la1k/la1k-cw-beacon/img/DSC_0003.jpg

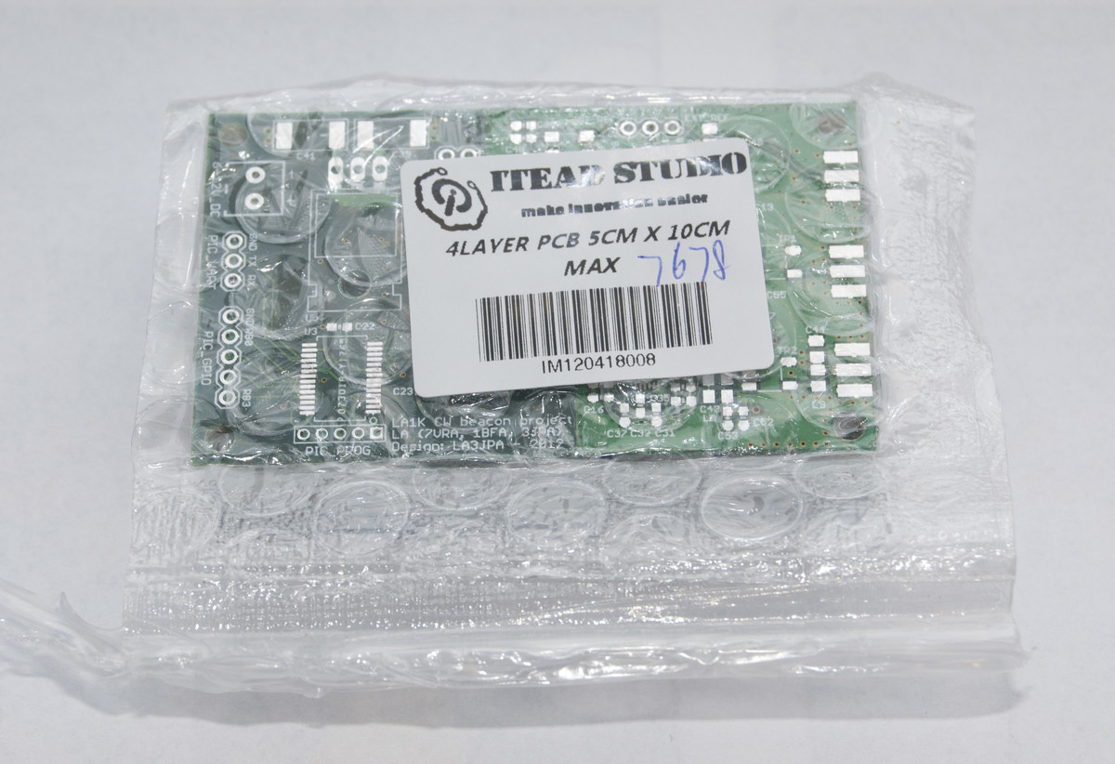
img/DSC_0003.jpg
