la1k/la1k-cw-beacon/img/DSC_0007.jpg

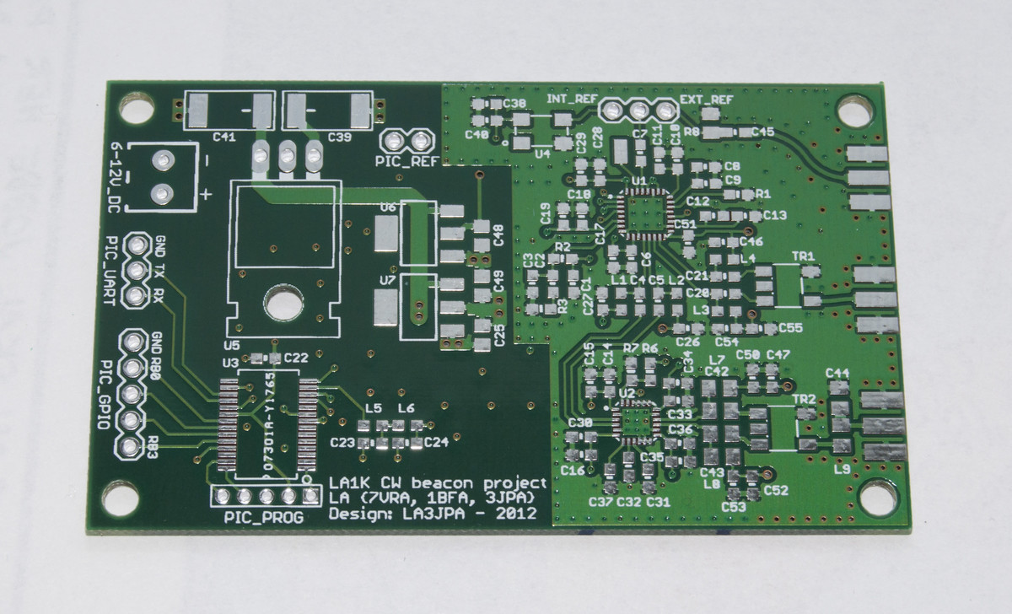
img/DSC_0007.jpg
