la1k/la1k-cw-beacon/img/IMAG1740.jpg

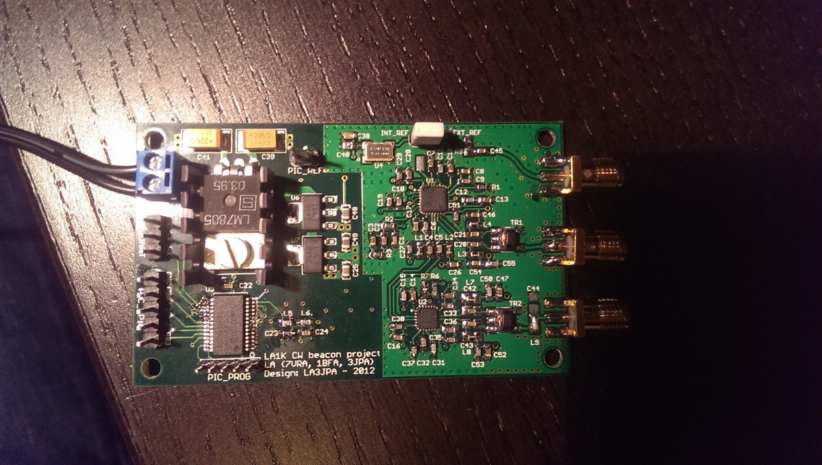
img/IMAG1740.jpg
