la1k/la1k-cw-beacon/img/IMAG1915.jpg

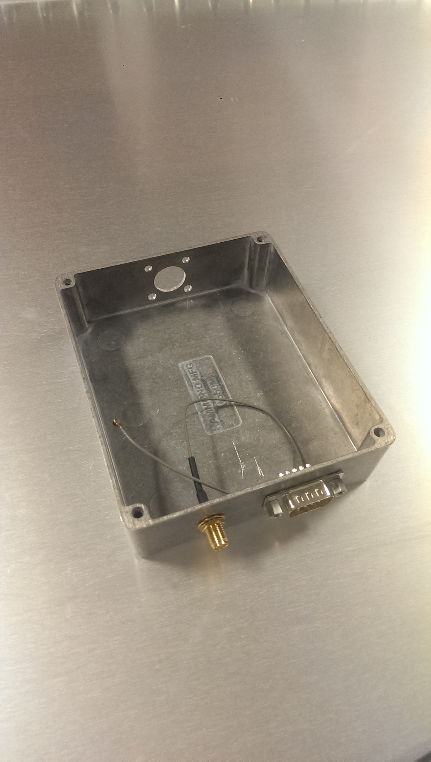
img/IMAG1915.jpg
