la1k/la1k-cw-beacon/img/IMAG2300.jpg

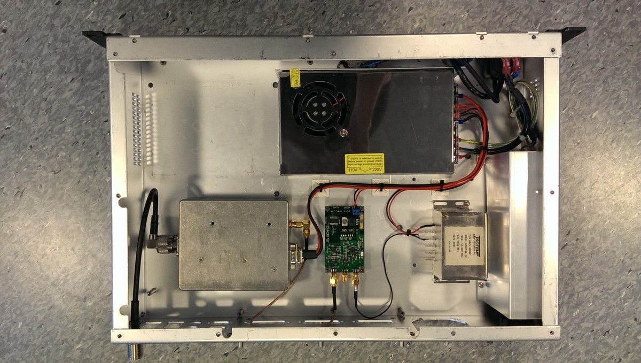
img/IMAG2300.jpg
