la1k/la1k-cw-beacon/img/la2uhf/IMAG2589.jpg

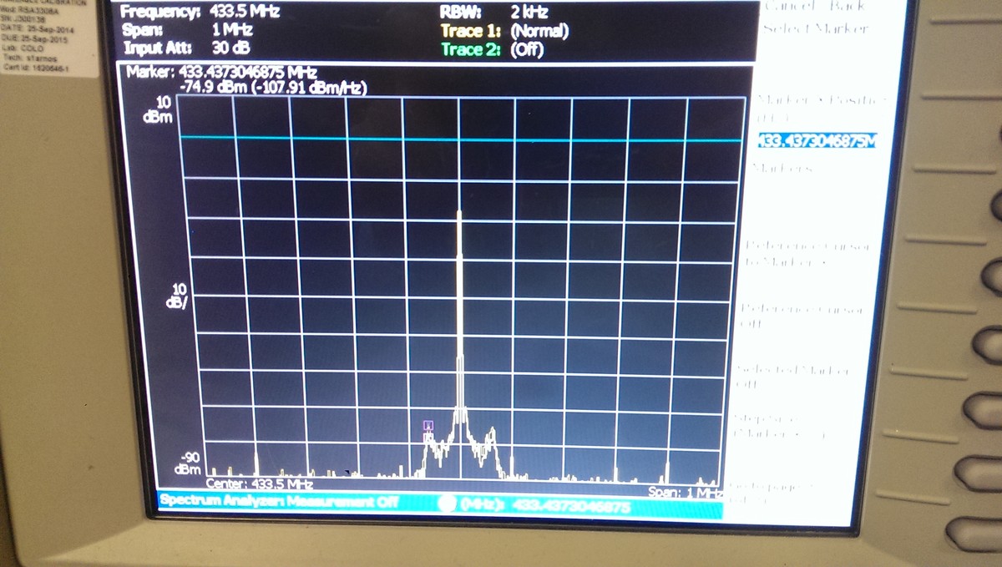
img/la2uhf/IMAG2589.jpg
