la1k/la1k-cw-beacon/img/la2uhf/IMAG2644.jpg

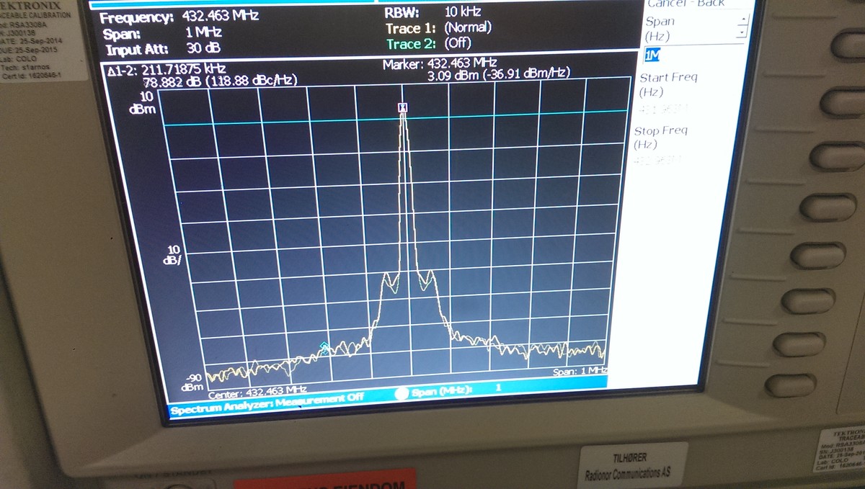
img/la2uhf/IMAG2644.jpg
