la1k/la1k-cw-beacon/img/signal_fra_ref.jpg

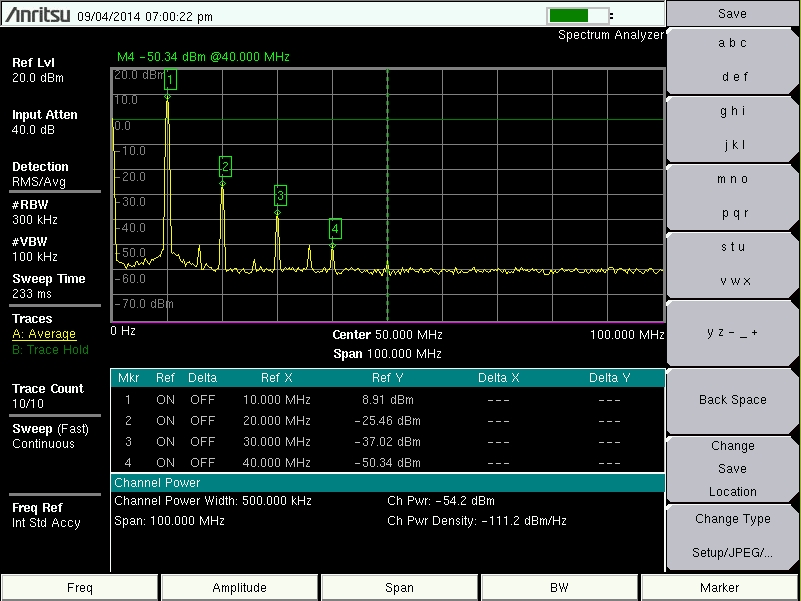
img/signal_fra_ref.jpg
