la1k/la1k-cw-beacon/img/signal_fra_synth.jpg

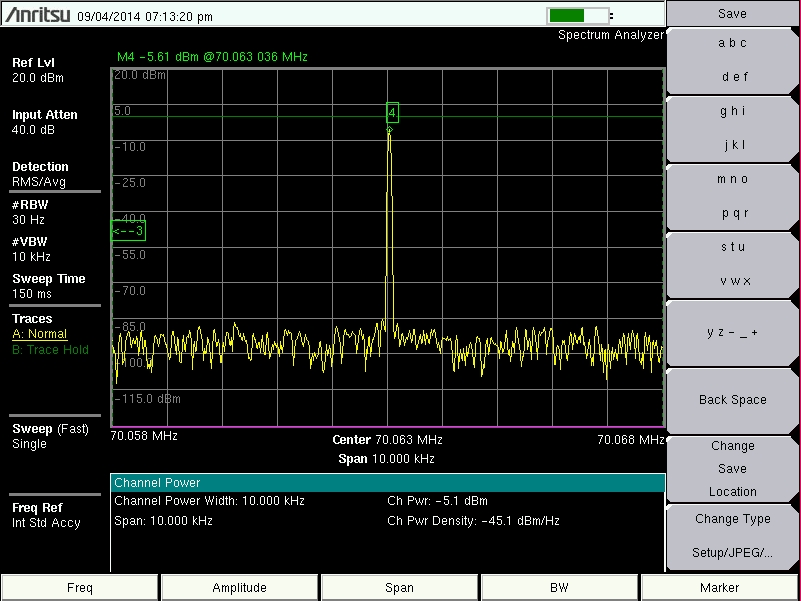
img/signal_fra_synth.jpg
