la1k/la1k-cw-beacon/other/70_mhz/pa_design/pmpa_components.png

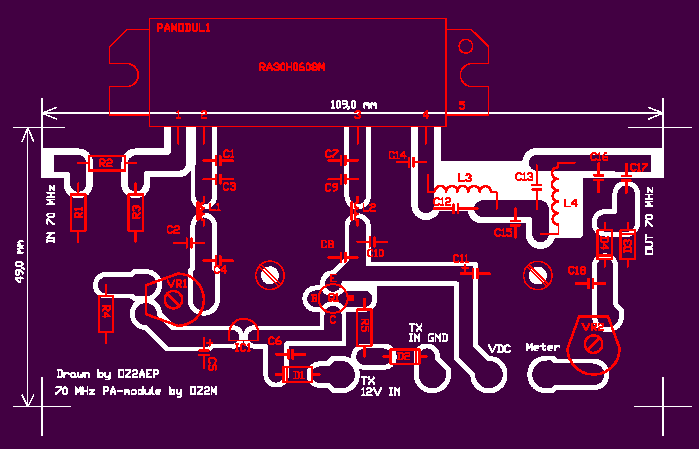
other/70_mhz/pa_design/pmpa_components.png
