la1k/la1k-cw-beacon/firmware/spi.h

//**************************************************************//
// LA1K CW beacon - Jon Petter Skagmo, LA3JPA, 2013.            //
// Licensed under LGPL.                                         //
//**************************************************************//

#ifndef SPI_H
#define	SPI_H

void spi(char data);

#endif	/* SPI_H */
